mateolavandera/DIMECRES_ML_AL_SEIENTS/Conversor senyal temperatura.asc

R1: res; 9k
R2: res; 1k
R3: res; 100k
U2: LT1638
V1: voltage; 5
V2: voltage; 1
V3: voltage; -5
Named nets: 0, V+, ANALOGIC_OUT, V-
.dc V2 20m 600m
