mateolavandera/DIMECRES_ML_AL_SEIENTS/Final_de_carrera.asc

IN_FC: voltage; 1
Micro: voltage; 5
R1: res; 10k
R2: res; 10k
R3: res; 10k
U1: opamp2; LM393
V1: voltage; 5
Named nets: 0, +V, OUT_FC
.inc LM393.5_1
.dc IN_FC 0 10
