mateolavandera/DIMECRES_ML_AL_SEIENTS/ReguladorLineal.asc

C1: polcap; 1µ
C2: cap; 100n
C3: cap; 10µ
C4: polcap; 1µ
C5: cap; 100n
D1N4002: diode
D1N4733A: zener
R1: res; 120; tol=5
R2: res; 360; tol=5
U2: LT1086
V1: voltage; PULSE(0 12 0 10m 0 100m 200m)
Named nets: 0, +5V, VBAT
.model D1N4002 D (IS=5u N=1.7 RS=0.01 BV=100 IBV=5u CJO=20p)
.model D1N4733A D (BV=6 IBV=5u IS=1p N=1.5 RS=0.1)
.tran 0 50m 5m
